JGAguado/Smart-bike/Documentation/Silkscreen/Top.bmp

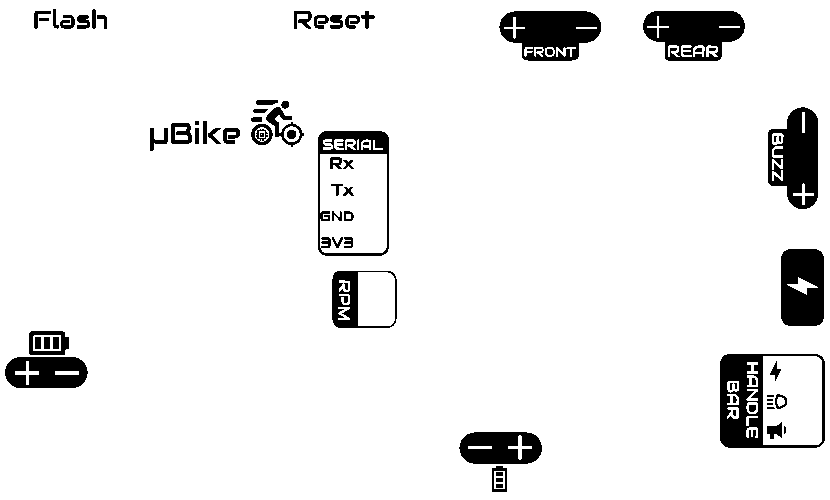
Documentation/Silkscreen/Top.bmp
